ssyhy9-Hongyu/Isolated-Buck/PCB CW/PCB CW 2/EEEE2046_PCB_Template(1)/PCBfootprints.pdf

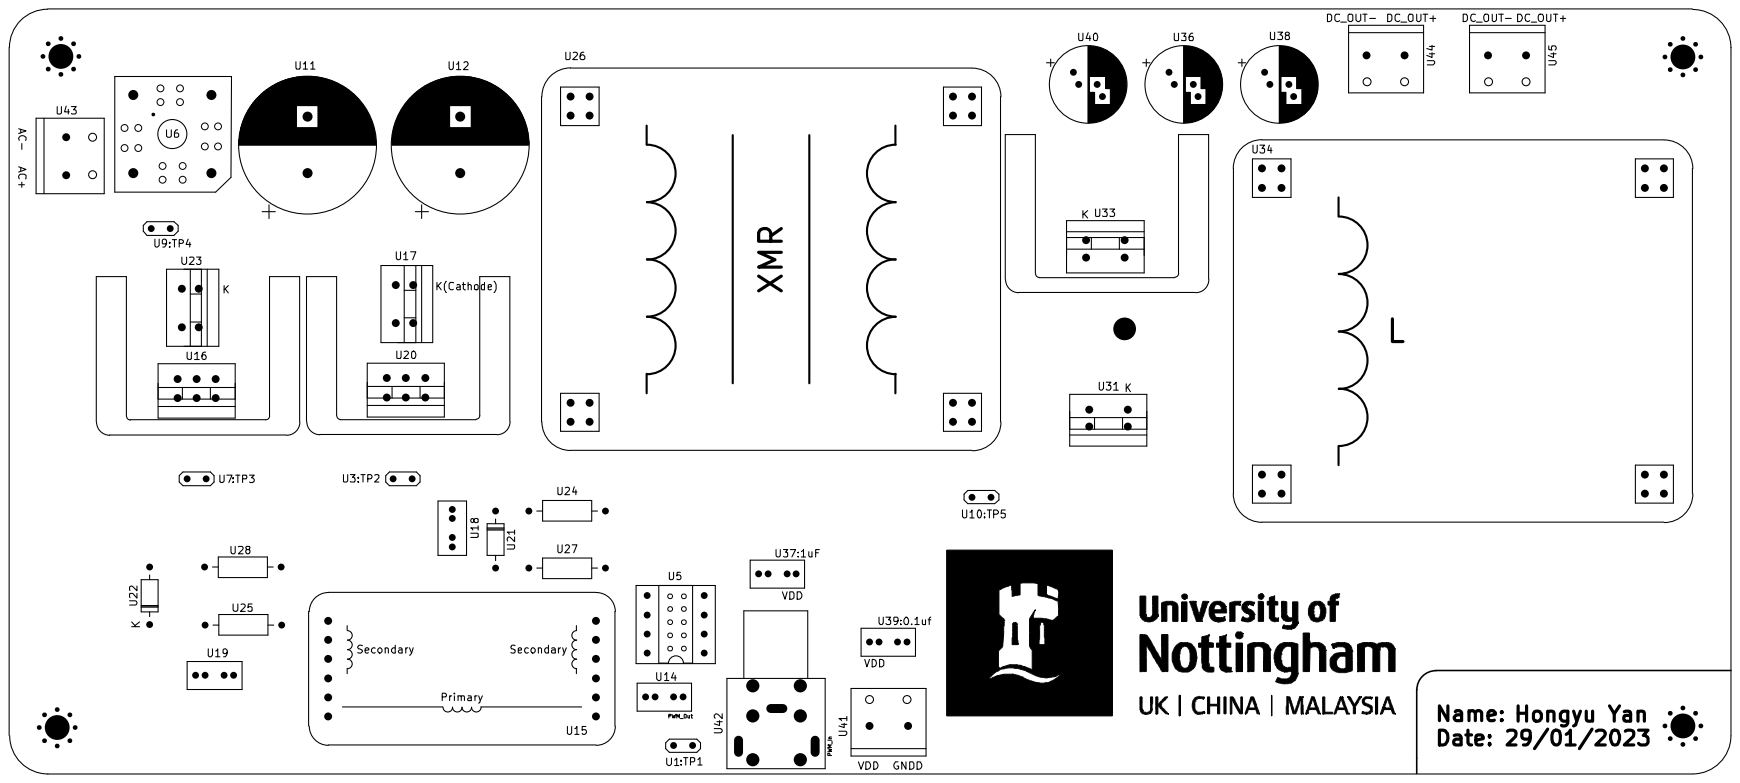
[picture p40: page 1]

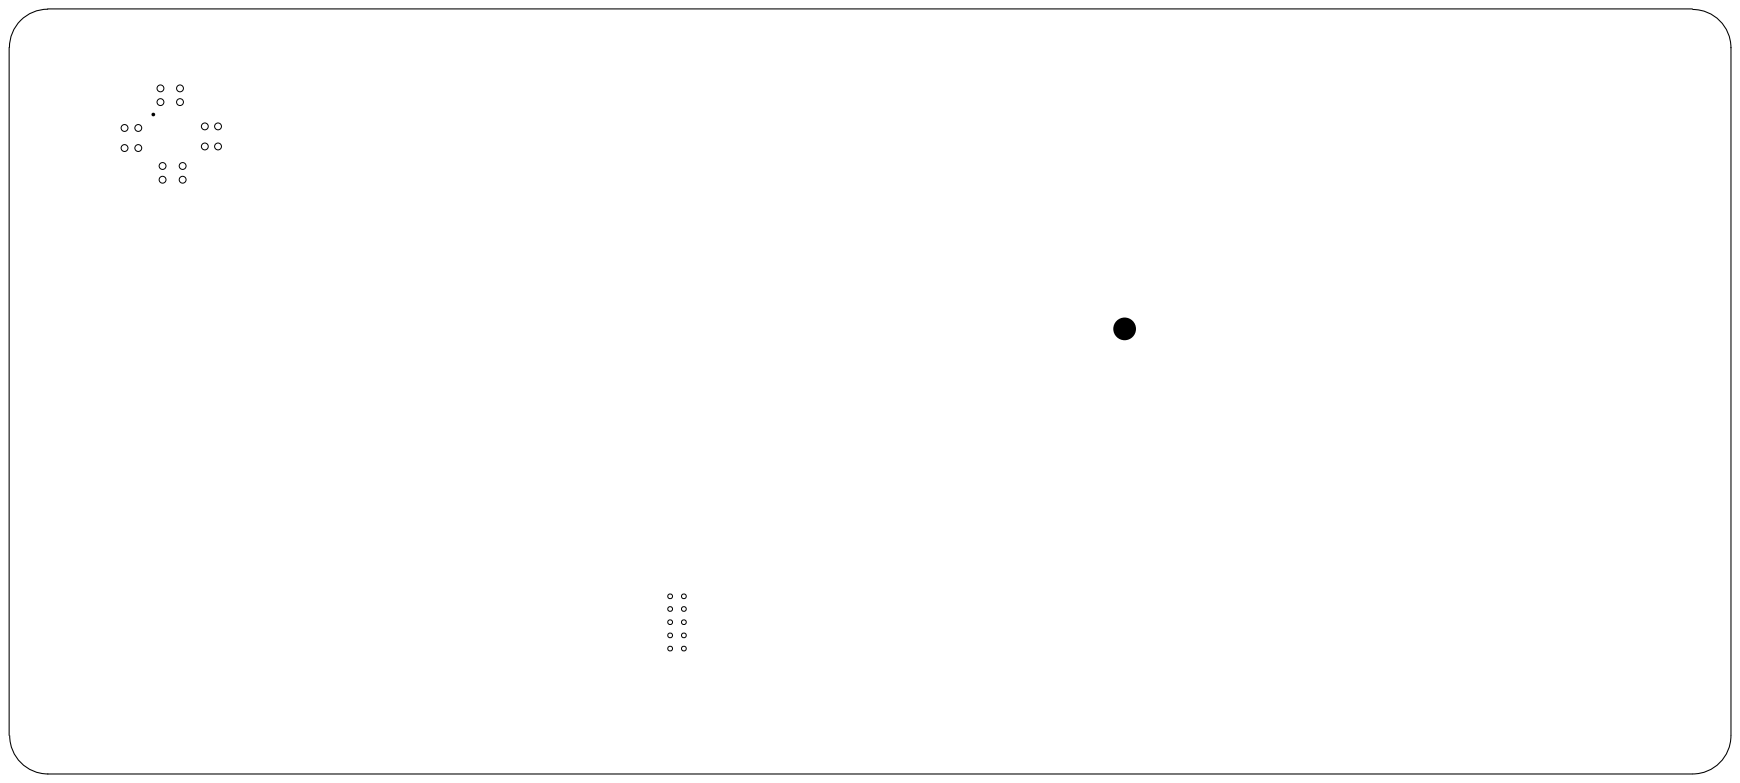
[picture p41: page 2]
